Xinyuan-LilyGO/LilyGo-T-OI-PLUS/example/simple/simple.ino

// How many NeoPixels are attached to the Arduino?
#define NUMPIXELS 7
#include <Adafruit_NeoPixel.h>
#ifdef __AVR__
  #include <avr/power.h>
#endif

//set pin
#define D1   19
#define D2   18
#define D3   9
#define D4   8
#define D5   5
#define D6   6
#define D7   7
#define D8   10


//D1 indicates that the dial switch 1 dials down to enable RGB .D2表示2。 D2 is 2.And so on....
#define PIN   D1
#define NUMPIXELS 7

Adafruit_NeoPixel pixels(NUMPIXELS, PIN, NEO_GRB + NEO_KHZ800);
#define DELAYVAL 500

void setup() {
#if defined(__AVR_ATtiny85__) && (F_CPU == 16000000)
  clock_prescale_set(clock_div_1);
#endif

  pixels.begin();
  pixels.show();            // Turn OFF all pixels ASAP
  pixels.setBrightness(50); // Set BRIGHTNESS to about 1/5 (max = 255)
}

void loop() {
  pixels.clear();

  for(int i=0; i<NUMPIXELS; i++) {

    pixels.setPixelColor(i, pixels.Color(0, 150, 0));
    pixels.show();
    delay(DELAYVAL);
  }
}
